cnvogelg/DiskFreezerX/sampler/sam7x/hardware/dfx-main-brd.png

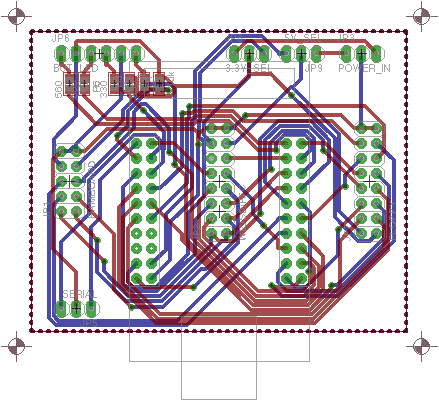
sampler/sam7x/hardware/dfx-main-brd.png
