cnvogelg/DiskFreezerX/sampler/sam7x/hardware/dfx-main-sch.png

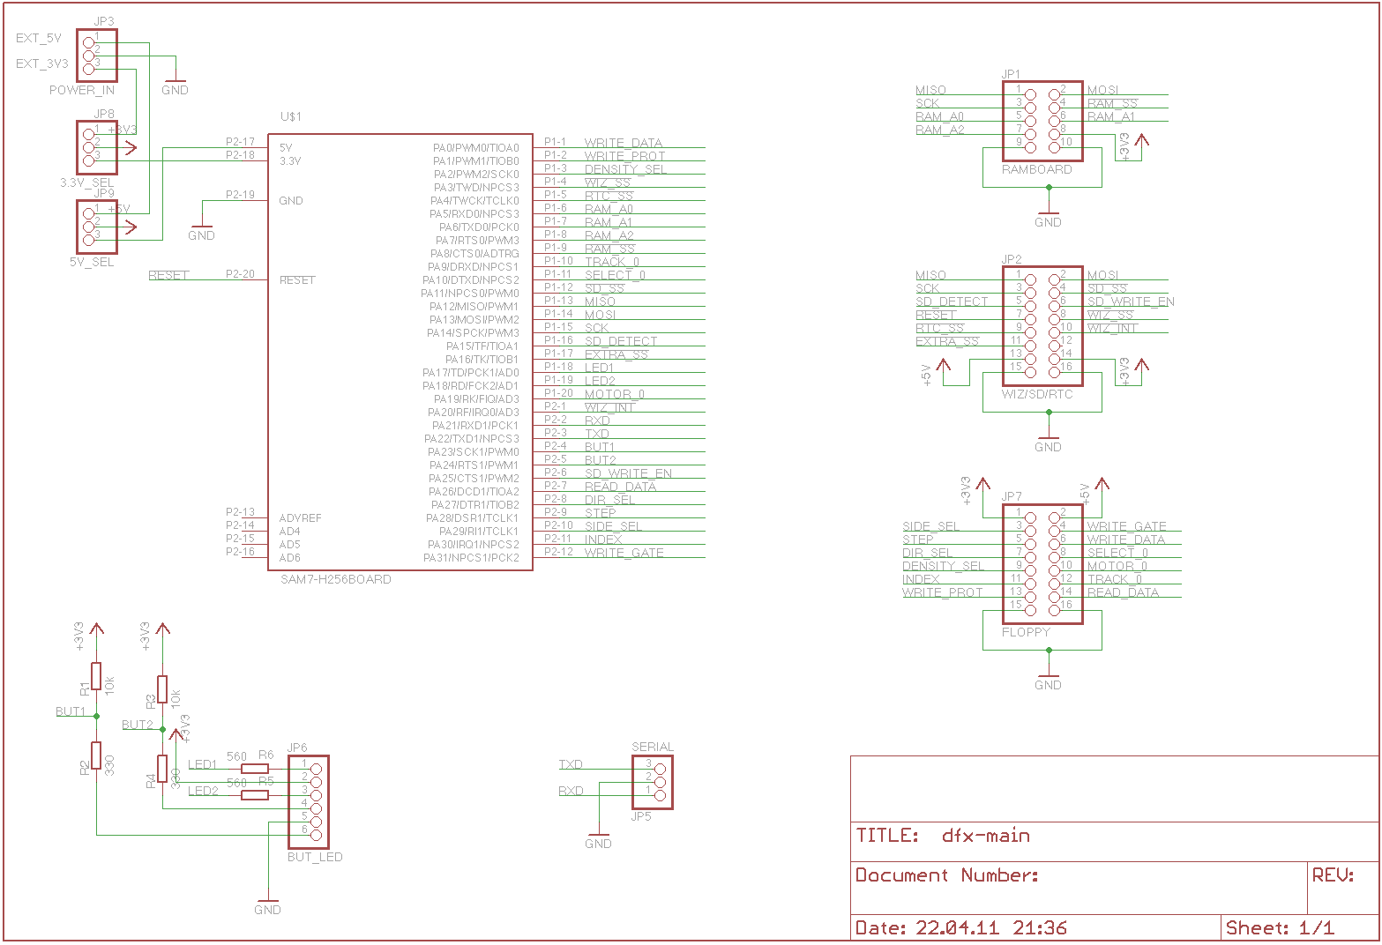
sampler/sam7x/hardware/dfx-main-sch.png
