cnvogelg/DiskFreezerX/sampler/avr/topaz.c

/*
 * Amiga TopazPlus Font
 *
 * Converted from "TopazPlus a600a1200a400" from
 * http://www.trueschool.org/
 * 
 * File download:
 * http://www.trueschool.org/files/fonts/t!s-af10.zip
 *
 *    Topaz is © AmigaInc.
 *    ttf, fon, eot, raw & psf v1/v2 versions of Topaz are © dMG/t!s^dS!
 *    ttf, fon, eot, raw & psf v1/v2 versions of TopazPlus are © dMG/t!s^dS!
 *
 */

#include "topaz.h"

const prog_uint8_t topaz_font_PGM[4096] = {
           0x00,0x00,0x00,0x00,0x00,0x00,0x00,0x00,0x00,0x00,0x00,0x00,0x00,0x00,0x00,0x00,
           0x83,0x83,0x39,0x39,0x21,0x21,0x29,0x29,0x21,0x21,0x3f,0x3f,0x87,0x87,0xff,0xff,
           0xc3,0xc3,0x99,0x99,0x99,0x99,0x81,0x81,0x99,0x99,0x99,0x99,0x99,0x99,0xff,0xff,
           0x83,0x83,0x99,0x99,0x99,0x99,0x83,0x83,0x99,0x99,0x99,0x99,0x83,0x83,0xff,0xff,
           0xe1,0xe1,0xcf,0xcf,0x9f,0x9f,0x9f,0x9f,0x9f,0x9f,0xcf,0xcf,0xe1,0xe1,0xff,0xff,
           0x87,0x87,0x93,0x93,0x99,0x99,0x99,0x99,0x99,0x99,0x93,0x93,0x87,0x87,0xff,0xff,
           0x81,0x81,0x9f,0x9f,0x9f,0x9f,0x87,0x87,0x9f,0x9f,0x9f,0x9f,0x81,0x81,0xff,0xff,
           0x81,0x81,0x9f,0x9f,0x9f,0x9f,0x87,0x87,0x9f,0x9f,0x9f,0x9f,0x9f,0x9f,0xff,0xff,
           0xc3,0xc3,0x99,0x99,0x9f,0x9f,0x91,0x91,0x99,0x99,0x99,0x99,0xc1,0xc1,0xff,0xff,
           0x99,0x99,0x99,0x99,0x99,0x99,0x81,0x81,0x99,0x99,0x99,0x99,0x99,0x99,0xff,0xff,
           0xc3,0xc3,0xe7,0xe7,0xe7,0xe7,0xe7,0xe7,0xe7,0xe7,0xe7,0xe7,0xc3,0xc3,0xff,0xff,
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
           0x03,0x03,0x66,0x66,0xac,0xac,0xd8,0xd8,0x36,0x36,0x6a,0x6a,0xcc,0xcc,0x00,0x00,
           0x38,0x38,0x6c,0x6c,0x68,0x68,0x76,0x76,0xdc,0xdc,0xce,0xce,0x7b,0x7b,0x00,0x00,
           0x18,0x18,0x18,0x18,0x30,0x30,0x00,0x00,0x00,0x00,0x00,0x00,0x00,0x00,0x00,0x00,
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
};
